squaregolab/EasyHomeConcept/Sources/InterfacePi/src/extfx/scene/control/doc-files/DatePicker.png

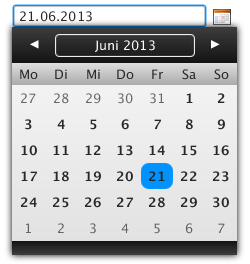
Sources/InterfacePi/src/extfx/scene/control/doc-files/DatePicker.png
