squaregolab/EasyHomeConcept/Sources/Modeles sketchups/ventilo/dessin-1.dxf

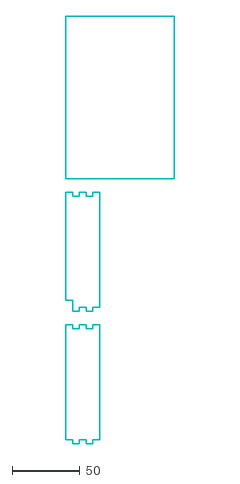
[picture p22: CAD file, 2017-02-01]
Sources/Modeles sketchups/ventilo/dessin-1.dxf
80.0 x 316.0
