squaregolab/EasyHomeConcept/Sources/Modeles sketchups/coupleur moteur/coupleur moteur0.stl

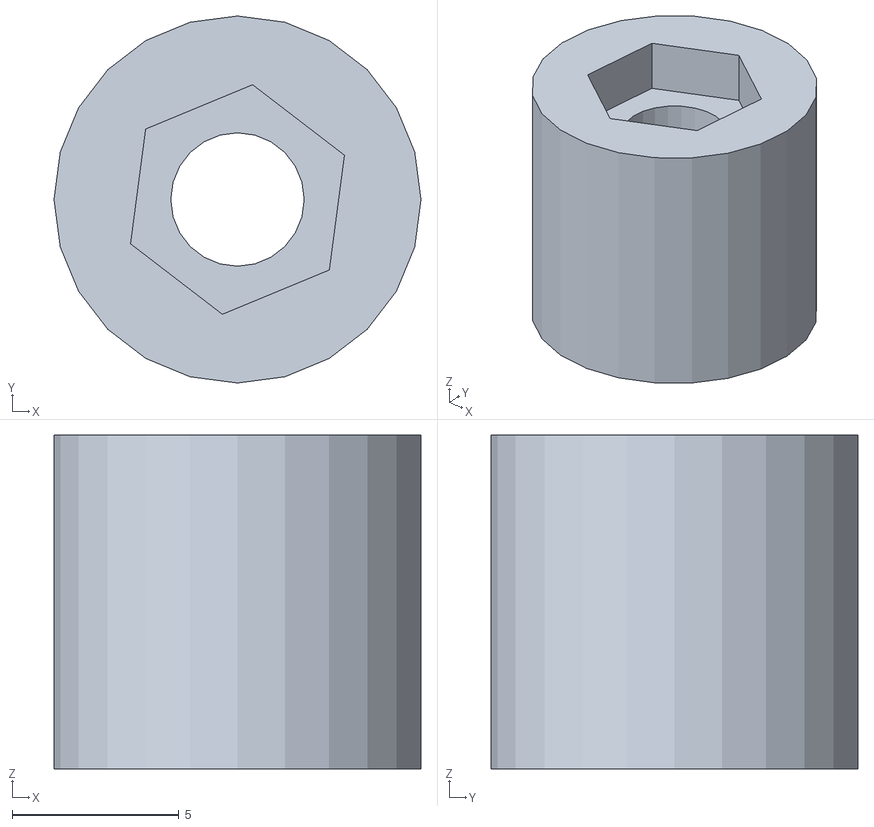
[picture p23: CAD file, 2017-02-01]
Sources/Modeles sketchups/coupleur moteur/coupleur moteur0.stl
11.0 x 11.0 x 10.0
