squaregolab/EasyHomeConcept/Sources/Modeles sketchups/Maquette maison/plaque5.dxf

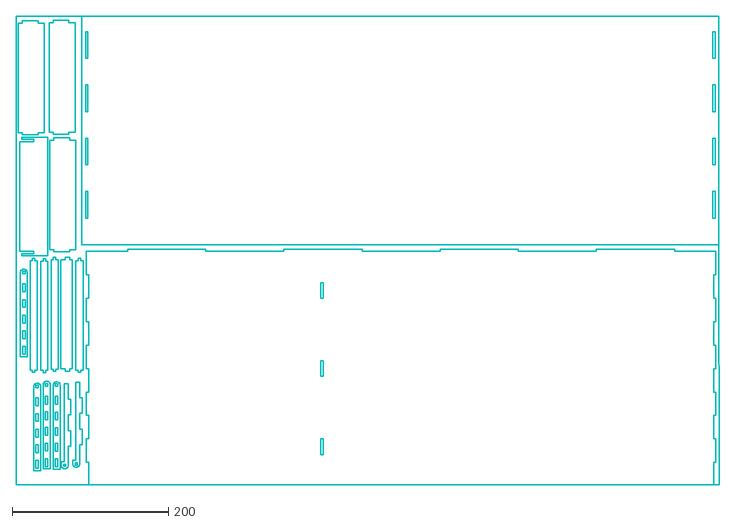
[picture p24: CAD file, 2017-02-01]
Sources/Modeles sketchups/Maquette maison/plaque5.dxf
900.0 x 600.0
