squaregolab/EasyHomeConcept/Sources/Modeles sketchups/Meuble/tapis.dxf

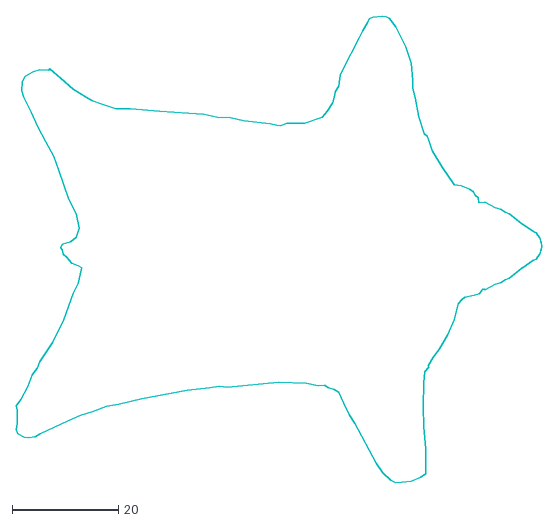
[picture p25: CAD file, 2017-02-01]
Sources/Modeles sketchups/Meuble/tapis.dxf
99.0 x 87.8
