squaregolab/EasyHomeConcept/Sources/Modeles sketchups/coupleur moteur/coupleur moteur1.stl

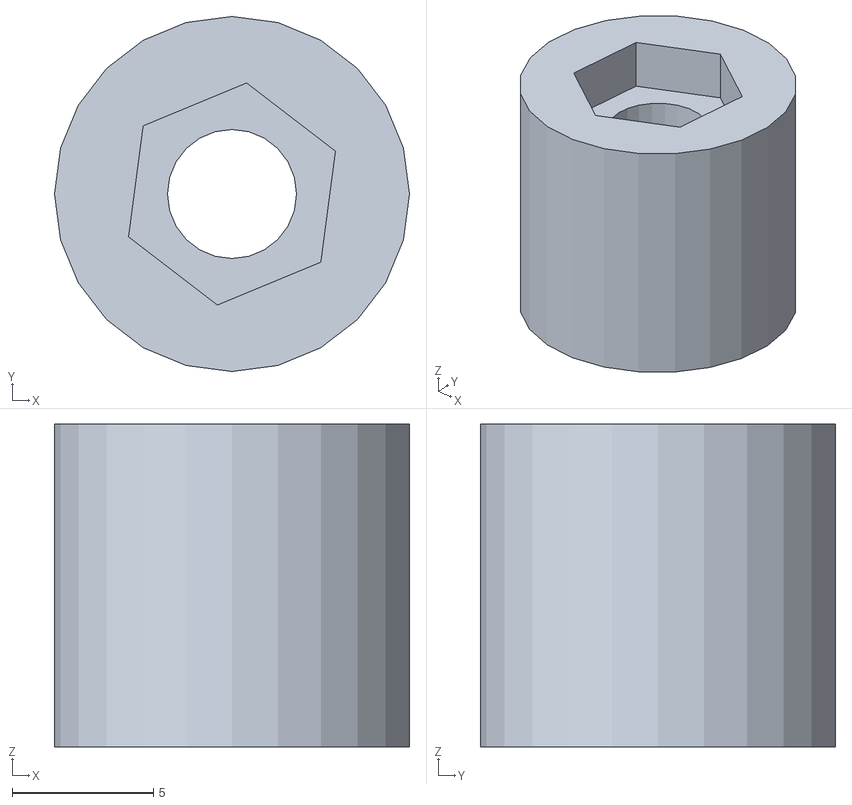
[picture p26: CAD file, 2017-02-01]
Sources/Modeles sketchups/coupleur moteur/coupleur moteur1.stl
12.6 x 12.6 x 11.4
