squaregolab/EasyHomeConcept/Sources/Modeles sketchups/Maquette maison/plaque3.dxf

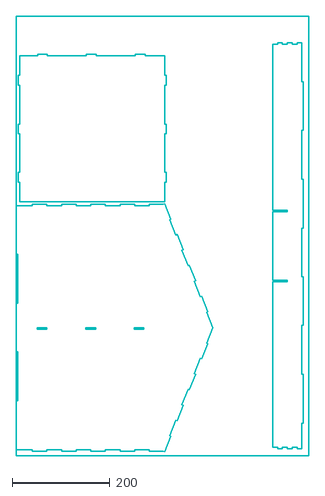
[picture p27: CAD file, 2017-02-01]
Sources/Modeles sketchups/Maquette maison/plaque3.dxf
600.0 x 900.0
