squaregolab/EasyHomeConcept/Sources/Modeles sketchups/Meuble/dessin3.dxf

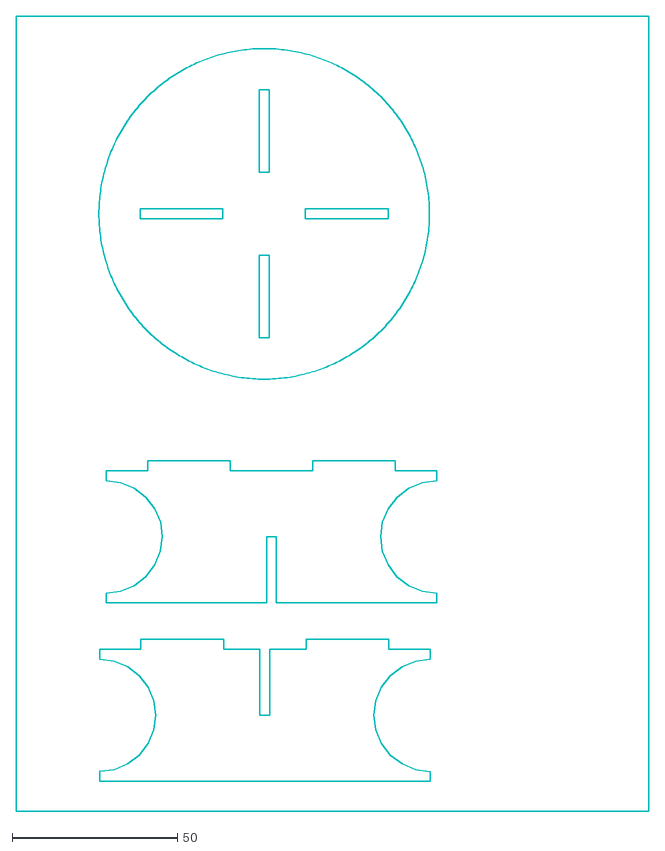
[picture p28: CAD file, 2017-02-01]
Sources/Modeles sketchups/Meuble/dessin3.dxf
191.4 x 240.5
