squaregolab/EasyHomeConcept/Sources/Modeles sketchups/Maquette maison/plaque2.dxf

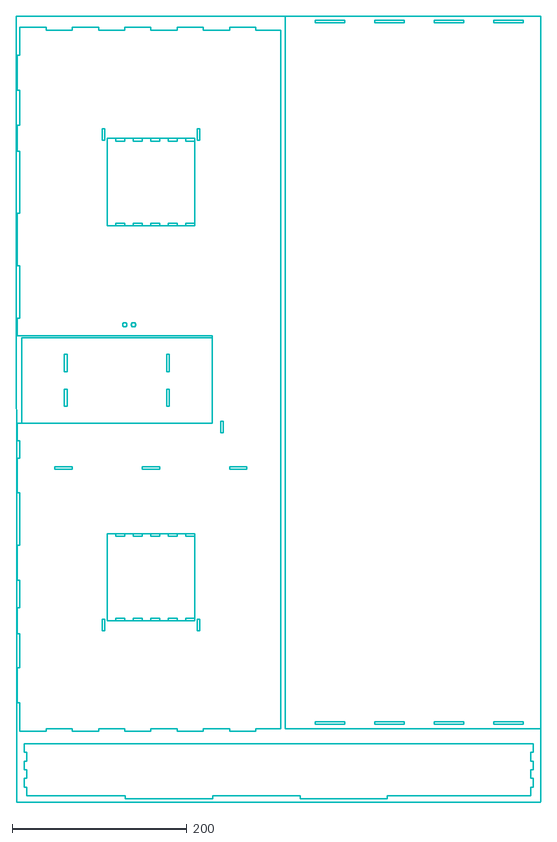
[picture p29: CAD file, 2017-02-01]
Sources/Modeles sketchups/Maquette maison/plaque2.dxf
601.0 x 900.0
