squaregolab/EasyHomeConcept/Sources/Modeles sketchups/Meuble/tapis2.dxf

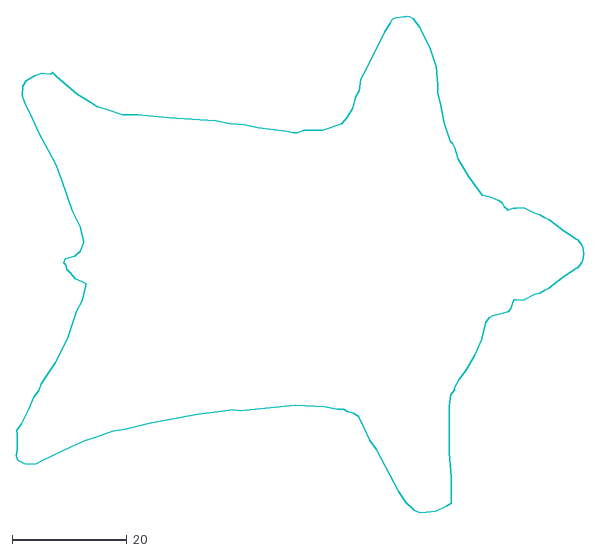
[picture p30: CAD file, 2017-02-01]
Sources/Modeles sketchups/Meuble/tapis2.dxf
99.0 x 86.5
