squaregolab/EasyHomeConcept/Sources/Modeles sketchups/Meuble/dessin2.dxf

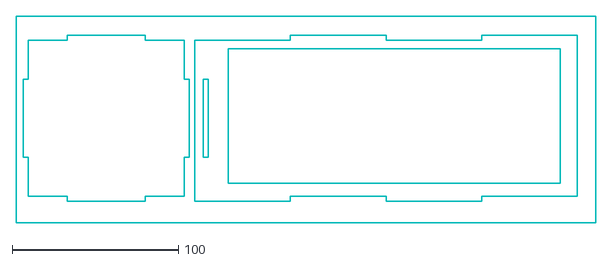
[picture p31: CAD file, 2017-02-01]
Sources/Modeles sketchups/Meuble/dessin2.dxf
349.0 x 124.0
